UselessPickles/diamondtel-m92-bluetooth/microcontroller/DiamondTelM92Bluetooth.X/src/bluetooth/bt_command_send.c

/******************************************************************************
 Software License Agreement:

 The software supplied herewith by Microchip Technology Incorporated
 (the "Company") for its PICmicro(r) Microcontroller is intended and
 supplied to you, the Company's customer, for use solely and
 exclusively on Microchip PICmicro Microcontroller products. The
 software is owned by the Company and/or its supplier, and is
 protected under applicable copyright laws. All rights are reserved.
 Any use in violation of the foregoing restrictions may subject the
 user to criminal sanctions under applicable laws, as well as to
 civil liability for the breach of the terms and conditions of this
 license.

 THIS SOFTWARE IS PROVIDED IN AN "AS IS" CONDITION. NO WARRANTIES,
 WHETHER EXPRESS, IMPLIED OR STATUTORY, INCLUDING, BUT NOT LIMITED
 TO, IMPLIED WARRANTIES OF MERCHANTABILITY AND FITNESS FOR A
 PARTICULAR PURPOSE APPLY TO THIS SOFTWARE. THE COMPANY SHALL NOT,
 IN ANY CIRCUMSTANCES, BE LIABLE FOR SPECIAL, INCIDENTAL OR
 CONSEQUENTIAL DAMAGES, FOR ANY REASON WHATSOEVER.
********************************************************************/
#include "bt_command_send.h"
#include "bt_command_decode.h"
#include "atcmd.h"
#include <xc.h>
#include <string.h>
#include <stdio.h>
#include "../../mcc_generated_files/uart2.h"
#include "../../mcc_generated_files/pin_manager.h"
#include "../app.h"

#define ACK_TIME_OUT_MS                 1000
#define APP_INPUT_WAITING_TIME_OUT_MS   100
#define INTERVAL_AFTER_ACK_CMD          20
#define QUEQUED_CMD_MAX                 20

static struct {
    uint8_t SendingCmdNum;
    struct{
        uint16_t startBufPt;
        uint16_t endBufPt;
        uint16_t cmdSize;
        uint8_t cmdID;
		uint8_t cmdInfo;
        CMD_PROCESSING_STATUS cmdStatus;
    } SendingCmdArray[QUEQUED_CMD_MAX];
} BT_SendingCmd;

#define UR_TX_BUF_SIZE              400
static uint8_t          UR_TxBuf[UR_TX_BUF_SIZE];
static uint16_t         UR_TxBufHead;
static uint16_t         UR_TxBufTail;
static uint16_t         UR_TxBufTail2;
typedef enum {
	TXRX_BUF_EMPTY,
	TXRX_BUF_OK,
	TXRX_BUF_FULL
} TXRX_BUF_STATUS;
static TXRX_BUF_STATUS  UR_TxBufStatus;

typedef enum {
    BT_CMD_SEND_STATE_IDLE = 0,         //no data in the queue, MFB is low
    BT_CMD_SEND_MFB_HIGH_WAITING,       //set MFB to high, and wait for 2ms
    BT_CMD_SEND_DATA_SENDING,           //UART interface is working
    BT_CMD_SEND_ACK_WAITING,            //waiting for ack
    BT_CMD_SEND_ACK_ERROR,
    BT_CMD_SEND_ACK_OK,
} BT_CMD_SEND_STATE;
BT_CMD_SEND_STATE BT_CMD_SendState;
uint16_t BT_CommandSendTimer;//BT_CommandStartMFBWaitTimer;
uint16_t BT_commandOverRun=0;
uint16_t BT_bufferOverRun=0;
uint8_t gatt_status_code=0;

static bool copyCommandToBuffer(uint8_t* data, uint16_t size, uint8_t cmdInfo);
static bool StartRegisterNewCommand(uint16_t start_index, uint16_t cmd_size, uint8_t cmd_id, uint8_t cmd_info);
static bool EndRegisterNewCommand(uint16_t end_index);
static bool RemoveFirstCommand(void);

/*======================================*/
/*  function implemention  */
/*======================================*/
void BT_GiveUpThisCommand( void )
{
    RemoveFirstCommand();
}
/*------------------------------------------------------------*/

/*------------------------------------------------------------*/
bool copySendingCommandToBuffer(uint8_t* data, uint16_t size)
{
	return copyCommandToBuffer(data, size, CMD_INFO_MCU);
}
static bool copyCommandToBuffer(uint8_t* data, uint16_t size, uint8_t cmdInfo)
{
    bool buf_result = true;
    uint8_t ur_tx_buf_status_save = UR_TxBufStatus;
    uint16_t ur_tx_buf_head_save = UR_TxBufHead;

	if(UR_TxBufHead > UR_TxBufTail)
	{
		if(UR_TxBufHead - UR_TxBufTail	+ size >= UR_TX_BUF_SIZE)
		{
			BT_bufferOverRun++;
			return false;		
		}
	}	
	else if(UR_TxBufHead < UR_TxBufTail)
	{
		if(UR_TxBufHead + size >=  UR_TxBufTail)
		{
			BT_bufferOverRun++;
			return false;
		}
	}

    if(UR_TxBufStatus !=  TXRX_BUF_FULL)
    {
        if(!StartRegisterNewCommand(UR_TxBufHead, size, data[3], cmdInfo))
        {
            return false;
        }
        
        while(size--)
        {
            UR_TxBuf[UR_TxBufHead++] = *data++;

            if(UR_TxBufHead >= UR_TX_BUF_SIZE)
                UR_TxBufHead = 0;

            if(UR_TxBufHead ==  UR_TxBufTail)
            {
                if(size)
                {
                    buf_result = false;
                    UR_TxBufStatus = ur_tx_buf_status_save;		//restore in this case
                    UR_TxBufHead = ur_tx_buf_head_save;                 //restore in this case
                }
                else
                {
                    UR_TxBufStatus =  TXRX_BUF_FULL;            //test this code
                }
                break;
            }
            else
            {
                UR_TxBufStatus = TXRX_BUF_OK;
            }
        }

        if(buf_result)
        {
            EndRegisterNewCommand(UR_TxBufHead);
        }
    }
    else
    {
        buf_result = false;
    }
    return buf_result;
}

/*------------------------------------------------------------*/

uint8_t BT_CalculateCmdChecksum(uint8_t const* startByte, uint8_t const* endByte)
{
    uint8_t checksum = 0;
    while(startByte <= endByte)
    {
        checksum += *startByte;
        startByte++;
    }
    checksum = ~checksum + 1;
    return checksum;
}

void BT_SendBytesAsCompleteCommand(uint8_t const* command, uint8_t command_length)
{
    copySendingCommandToBuffer(command, command_length);
}

/*------------------------------------------------------------*/

void BT_ResetEEPROM(void) {
  BT_MMI_ActionCommand(RESET_EEPROM_SETTING, BT_linkIndex);
}

void BT_SetEventMask(void) {
  uint8_t command[9];
  command[0] = 0xAA;                      //header byte 0
  command[1] = 0x00;                      //header byte 1
  command[2] = 5;                      //length
  command[3] = REPORT_MASK;        	//command ID
  command[4] = 0b00111011;
  command[5] = 0b01110000;     
  command[6] = 0b11110101;     
  command[7] = 0b11111111;     
  command[8] = BT_CalculateCmdChecksum(&command[2], &command[7]);
  copySendingCommandToBuffer(command, 9);  
}

void BT_ReadLinkedDeviceName(void) {
  uint8_t command[7];
  command[0] = 0xAA;                      //header byte 0
  command[1] = 0x00;                      //header byte 1
  command[2] = 3;                      //length
  command[3] = READ_LINKED_DEVICE_INFOR;   	//command ID
  command[4] = BT_linkIndex; // link_index, set to 0
  command[5] = 0; // 0 = read device name
  command[6] = BT_CalculateCmdChecksum(&command[2], &command[5]);
  copySendingCommandToBuffer(command, 7);  
}

void BT_ReadLocalBDAddress(void) {
  uint8_t command[7];
  command[0] = 0xAA;                      //header byte 0
  command[1] = 0x00;                      //header byte 1
  command[2] = 3;                      //length
  command[3] = READ_LOCAL_BD_ADDR;   	//command ID
  command[4] = BT_linkIndex; // link_index, set to 0
  command[5] = 0; // 0 = read device name
  command[6] = BT_CalculateCmdChecksum(&command[2], &command[5]);
  copySendingCommandToBuffer(command, 7);  
}

void BT_ReadDeviceName(void) {
  uint8_t command[6];
  command[0] = 0xAA;                      //header byte 0
  command[1] = 0x00;                      //header byte 1
  command[2] = 2;                      //length
  command[3] = READ_LOCAL_DEVICE_NAME;   	//command ID
  command[4] = 0; // reserved (set to zero)
  command[5] = BT_CalculateCmdChecksum(&command[2], &command[4]);
  copySendingCommandToBuffer(command, 6);  
}

bool BT_SetDeviceName(char const* name) {
  size_t len = strlen(name);
  
  if (len > BT_MAX_DEVICE_NAME_LENGTH) {
    return false;
  }
  
  uint8_t command[BT_MAX_DEVICE_NAME_LENGTH + 8];
  command[0] = 0xAA;      //header byte 0
  command[1] = 0x00;      //header byte 1
  command[2] = len + 4;      //length
  command[3] = CONFIGURE_VENDOR_PARAMETER;      //command ID
  command[4] = 0;      // op code: 0 = set device name
  command[5] = 0;      // option (reserved): set to zero
  command[6] = len;      // device name length


  memcpy(command + 7, name, len);

  command[len + 7] = BT_CalculateCmdChecksum(&command[2], &command[len + 6]);
	return copySendingCommandToBuffer(command, len + 8); 
}

bool BT_SetPinCode(uint8_t digit1, uint8_t digit2, uint8_t digit3, uint8_t digit4) {
  uint8_t command[9];
  command[0] = 0xAA;      //header byte 0
  command[1] = 0x00;      //header byte 1
  command[2] = 5;      //length
  command[3] = CHANGE_PIN_CODE;      //command ID
  command[4] = '0' + digit1;
  command[5] = '0' + digit2;
  command[6] = '0' + digit3;
  command[7] = '0' + digit4;
  command[8] = BT_CalculateCmdChecksum(&command[2], &command[7]);
	return copySendingCommandToBuffer(command, 9); 
}

void BT_StartVoiceCommand(void) {
  BT_MMI_ActionCommand(VOICE_DIAL, BT_linkIndex);
}

void BT_CancelVoiceCommand(void) {
  BT_MMI_ActionCommand(CANCEL_VOICE_DIAL, BT_linkIndex);
}

bool BT_MakeCall(char const* number) {
  printf("[CALL] Make Call: %s\r\n", number);
  
  size_t len = strlen(number);
  
  if (len > 19) {
    return false;
  }
  
  uint8_t command[25];
  command[0] = 0xAA;      //header byte 0
  command[1] = 0x00;      //header byte 1
  command[2] = len + 2;      //length
  command[3] = MAKE_CALL;      //command ID
  command[4] = BT_linkIndex;      //link_index, set to 0

  memcpy(command + 5, number, len);

  command[len + 5] = BT_CalculateCmdChecksum(&command[2], &command[len + 4]);
	return copySendingCommandToBuffer(command, len + 6);
}

void BT_SetMicrohponeMuted(bool isMuted) {
  BT_MMI_ActionCommand(isMuted ? MUTE_MIC : UNMUTE_MIC, BT_linkIndex);
}

void BT_EndCall(void) {
  printf("[CALL] End Call\r\n");
  BT_MMI_ActionCommand(FORCE_END_CALL, BT_linkIndex);
}

void BT_AcceptCall(void) {
  printf("[CALL] Accept Call\r\n");
  BT_MMI_ActionCommand(ACCEPT_CALL, BT_linkIndex);
}

void BT_RejectCall(void) {
  printf("[CALL] Reject Call\r\n");
  BT_MMI_ActionCommand(REJECT_CALL, BT_linkIndex);
}

void BT_SwapHoldOrWaitingCall(void) {
  printf("[CALL] Swap Hold/Waiting Call\r\n");
  BT_MMI_ActionCommand(ACTIVE_CALL_HOLD_ACCEPT_HELD_CALL, BT_linkIndex);
}

void BT_EndHoldOrWaitingCall(void) {
  printf("[CALL] End Hold/Waiting Call\r\n");
  BT_MMI_ActionCommand(RELEASE_CALL, BT_linkIndex);
}

void BT_SwapHoldOrWaitingCallAndEndActiveCall(void) {
  printf("[CALL] Swap Hold/Waiting Call + End Active Call\r\n");
  BT_MMI_ActionCommand(ACCEPT_WAITING_HOLD_CALL_RLS_ACTIVE_CALL, BT_linkIndex);
}

void BT_EnterPairingMode(void) {
  printf("[PAIR] Enter\r\n");
  BT_MMI_ActionCommand(ANY_MODE_ENTERING_PAIRING, 0);
}

void BT_ExitPairingMode(void) {
  printf("[PAIR] Exit\r\n");
  BT_MMI_ActionCommand(EXIT_PAIRING_MODE, 0);
}

void BT_MMI_ActionCommand(uint8_t MMI_ActionCode, uint8_t link_index)
{
	BT_Send_ActionCommand(MMI_ActionCode, link_index, CMD_INFO_MCU);
}

void BT_Send_ActionCommand(uint8_t MMI_ActionCode, uint8_t link_index, uint8_t cmd_info)
{
    uint8_t command[8];
    command[0] = 0xAA;      //header byte 0
    command[1] = 0x00;      //header byte 1
    command[2] = 0x03;      //length
    command[3] = MMI_CMD;      //command ID
    command[4] = link_index;      //link_index
    command[5] = MMI_ActionCode;
    command[6] = BT_CalculateCmdChecksum(&command[2], &command[5]);
  	copyCommandToBuffer(&command[0], 7, cmd_info);
    //CommandAckStatus.MMI_ACTION_status = COMMAND_IS_SENT;
}

/*------------------------------------------------------------*/
void BT_SendAckToEvent(uint8_t ack_event)
{
    uint8_t command[6];
    command[0] = 0xAA;                      //header byte 0
    command[1] = 0x00;                      //header byte 1
    command[2] = 0x02;                      //length
    command[3] = MCU_SEND_EVENT_ACK;        //command ID
    command[4] = ack_event;                 //event to ack
    command[5] = BT_CalculateCmdChecksum(&command[2], &command[4]);
    copySendingCommandToBuffer(&command[0], 6);
}

/*------------------------------------------------------------*/
void BT_LinkBackToLastDevice(void)
{
    printf("[LINKBACK] Start\r\n");
    uint8_t command[6];
    command[0] = 0xAA;                      //header byte 0
    command[1] = 0x00;                      //header byte 1
    command[2] = 0x02;                      //length
    command[3] = PROFILE_LINK_BACK;         //command ID
    command[4] = 0x01;                      //0x00: last device, 0x01: last HFP device, 0x02: last A2DP device
    command[5] = BT_CalculateCmdChecksum(&command[2], &command[4]);
    copySendingCommandToBuffer(&command[0], 6);
   // CommandAckStatus.LINK_BACK_status = COMMAND_IS_SENT;
}

/*------------------------------------------------------------*/
void BT_CancelLinkback(void)
{
    uint8_t command[6];
    command[0] = 0xAA;                      //header byte 0
    command[1] = 0x00;                      //header byte 1
    command[2] = 0x02;                      //length
    command[3] = DISCONNECT;                //command ID
    command[4] = 0x01;                      
    command[5] = BT_CalculateCmdChecksum(&command[2], &command[4]);
    copySendingCommandToBuffer(&command[0], 6);
}

/*------------------------------------------------------------*/
void BT_DisconnectAllProfile(void)
{
    uint8_t command[6];
    command[0] = 0xAA;                      //header byte 0
    command[1] = 0x00;                      //header byte 1
    command[2] = 0x02;                      //length
    command[3] = DISCONNECT;                //command ID
    command[4] = 0x0f;                      //event to ack
    command[5] = BT_CalculateCmdChecksum(&command[2], &command[4]);
    copySendingCommandToBuffer(&command[0], 6);
}
/*------------------------------------------------------------*/
void BT_SetHFPGain(uint8_t gain)
{
    uint8_t command[7];
    command[0] = 0xAA;                      //header byte 0
    command[1] = 0x00;                      //header byte 1
    command[2] = 0x03;                    //length
    command[3] = SET_HF_GAIN_LEVEL;                //command ID
    command[4] = BT_linkIndex;                      //link index
    command[5] = gain & 0x0f;
    command[6] = BT_CalculateCmdChecksum(&command[2], &command[5]);
  	copyCommandToBuffer(&command[0], 7, CMD_INFO_MCU);
}

/*------------------------------------------------------------*/
void BT_SetAecEnabled(bool isEnabled) {
  BT_MMI_ActionCommand(isEnabled ? ENABLE_AEC : DISABLE_AEC, BT_linkIndex);
}

/*------------------------------------------------------------*/
void BT_CommandSend_Initialize( void )
{
    UR_TxBufHead = 0;
    UR_TxBufTail = 0;
    UR_TxBufStatus = TXRX_BUF_EMPTY;
    BT_SendingCmd.SendingCmdNum = 0;
}

/*------------------------------------------------------------*/
void BT_CommandSend_Task( void )
{
    switch(BT_CMD_SendState)
    {
        case BT_CMD_SEND_STATE_IDLE:
            if(BT_SendingCmd.SendingCmdNum)
            {
                //IO_BT_MFB_SetHigh();
                BT_CommandSendTimer = 3;      //wait 2 - 3ms
                BT_CMD_SendState = BT_CMD_SEND_MFB_HIGH_WAITING;
            }
            break;
            
        case BT_CMD_SEND_MFB_HIGH_WAITING:
            if(!BT_CommandSendTimer)
            {
                UART_TransferFirstByte();
                BT_SendingCmd.SendingCmdArray[0].cmdStatus = IN_SENDING;
                BT_CMD_SendState = BT_CMD_SEND_DATA_SENDING;
            }
            break;

        case BT_CMD_SEND_DATA_SENDING:
            //do nothing, UART interrupt will handle
            break;

        case BT_CMD_SEND_ACK_WAITING:       //new
            if(!BT_CommandSendTimer)
            {
                APP_BT_EventHandler(BT_EVENT_CMD_SENT_NO_ACK, (uint16_t)(BT_SendingCmd.SendingCmdArray[0].cmdID),  0);        //send event to user application layer with command id, and event type
                
                if (BT_SendingCmd.SendingCmdArray[0].cmdID == VENDOR_AT_CMD) {
                  ATCMD_BT_ResponseHandler(ATCMD_Response_FAILED);
                }
                
                BT_SendingCmd.SendingCmdArray[0].cmdStatus = ERROR_NO_ACK;
                BT_CommandSendTimer = APP_INPUT_WAITING_TIME_OUT_MS;
                BT_CMD_SendState = BT_CMD_SEND_ACK_ERROR;
            }
            break;
        
        case BT_CMD_SEND_ACK_ERROR:
            if (!BT_CommandSendTimer) {
                if (BT_SendingCmd.SendingCmdNum) {
                    UART_TransferFirstByte();
                    BT_SendingCmd.SendingCmdArray[0].cmdStatus = IN_SENDING;
                    BT_CMD_SendState = BT_CMD_SEND_DATA_SENDING; //re-sending last command or sending next command
                } else {
                    // BM6X_MFB_SetLow();
                    BT_CMD_SendState = BT_CMD_SEND_STATE_IDLE;
                }
            }
            break;
       
        case BT_CMD_SEND_ACK_OK:
            if (!BT_CommandSendTimer) {
                RemoveFirstCommand();
                if (BT_SendingCmd.SendingCmdNum) {
                    UART_TransferFirstByte();
                    BT_SendingCmd.SendingCmdArray[0].cmdStatus = IN_SENDING;
                    BT_CMD_SendState = BT_CMD_SEND_DATA_SENDING;
                } else {
                    //IO_BT_MFB_SetLow();
                    BT_CMD_SendState = BT_CMD_SEND_STATE_IDLE;
                }
            }
            break;
            
        default:
            break;
    }
}

/*------------------------------------------------------------*/
uint8_t BT_UpdateAckStatusWhenReceived(uint8_t command_id, uint8_t ack_status)
{
  uint8_t params[2] = {
    command_id, ack_status
  };
  
    uint16_t temp;
    if( BT_CMD_SendState == BT_CMD_SEND_ACK_WAITING )
    {
        if(command_id == BT_SendingCmd.SendingCmdArray[0].cmdID)
            BT_SendingCmd.SendingCmdArray[0].cmdStatus = ack_status;

		// Here we can know what is the ACK status 5506 reply to the previous sent command.
        BT_CommandSendTimer = APP_INPUT_WAITING_TIME_OUT_MS;
        BT_CMD_SendState = BT_CMD_SEND_ACK_OK;

		if(command_id == GATT_CTRL)
			gatt_status_code = ack_status;
        
    APP_BT_EventHandler(ack_status == 0 ? BT_EVENT_CMD_SENT_ACK_OK : BT_EVENT_CMD_SENT_ACK_ERROR, (uint16_t)command_id, params);        //send event to user application layer with command id, and event type
    
    if ((ack_status != 0) && (command_id == VENDOR_AT_CMD)) {
      ATCMD_BT_ResponseHandler(ATCMD_Response_FAILED);
    }

		return BT_SendingCmd.SendingCmdArray[0].cmdInfo;
    }
	return CMD_INFO_IGNORE;
}

/*------------------------------------------------------------*/
void BT_CommandSend_Timer1MS_Interrupt(void)
{
    if( BT_CommandSendTimer/*BT_CommandStartMFBWaitTimer*/)
    {
        -- BT_CommandSendTimer/*BT_CommandStartMFBWaitTimer*/;
    }
}

/*------------------------------------------------------------*/
void UART_TransferFirstByte( void )
{
    uint8_t data;
    UR_TxBufTail2 = BT_SendingCmd.SendingCmdArray[0].startBufPt;
    data = UR_TxBuf[UR_TxBufTail2++];
    if(UR_TxBufTail2 >= UR_TX_BUF_SIZE)
            UR_TxBufTail2 = 0;
    UART2_Write(data);
}

/*------------------------------------------------------------*/
void UART_TransferNextByte( void )
{
    uint8_t data;
    if(UR_TxBufTail2 == BT_SendingCmd.SendingCmdArray[0].endBufPt)
    {
        if(BT_CMD_SendState == BT_CMD_SEND_DATA_SENDING)
        {
            if(BT_SendingCmd.SendingCmdArray[0].cmdID != MCU_SEND_EVENT_ACK)
            {
                BT_CommandSendTimer =  ACK_TIME_OUT_MS;
                BT_CMD_SendState = BT_CMD_SEND_ACK_WAITING;
            }
            else        //just sent is ACK_TO_EVENT command
            {
                BT_CommandSendTimer = INTERVAL_AFTER_ACK_CMD;
                BT_SendingCmd.SendingCmdArray[0].cmdStatus = STS_OK;
                BT_CMD_SendState = BT_CMD_SEND_ACK_OK;
            }
        }
    }
    else
    {
        data = UR_TxBuf[UR_TxBufTail2++];
        if(UR_TxBufTail2 >= UR_TX_BUF_SIZE)
            UR_TxBufTail2 = 0;
        UART2_Write(data);
    }
}

static bool StartRegisterNewCommand(uint16_t start_index, uint16_t cmd_size, uint8_t cmd_id, uint8_t cmdInfo)
{
    if(!cmd_size)
        return false;
    
    if(BT_SendingCmd.SendingCmdNum < QUEQUED_CMD_MAX)
    {
        BT_SendingCmd.SendingCmdArray[BT_SendingCmd.SendingCmdNum].startBufPt = start_index;
        BT_SendingCmd.SendingCmdArray[BT_SendingCmd.SendingCmdNum].cmdSize = cmd_size;
        BT_SendingCmd.SendingCmdArray[BT_SendingCmd.SendingCmdNum].cmdID = cmd_id;
        BT_SendingCmd.SendingCmdArray[BT_SendingCmd.SendingCmdNum].cmdInfo = cmdInfo;

        if(cmd_id!=0x1f)
            Nop();
        return true;
    }
    else
    {
	    BT_commandOverRun++;
        return false;
    }
}

static bool EndRegisterNewCommand(uint16_t end_index)
{
    if(BT_SendingCmd.SendingCmdNum < QUEQUED_CMD_MAX)
    {
        BT_SendingCmd.SendingCmdArray[BT_SendingCmd.SendingCmdNum].endBufPt = end_index;
        BT_SendingCmd.SendingCmdArray[BT_SendingCmd.SendingCmdNum].cmdStatus = IN_QUEUE;
        BT_SendingCmd.SendingCmdNum++;
    }
    return true;
}

static bool RemoveFirstCommand(void)//index starting from 0
{
    uint8_t i;
    if(!BT_SendingCmd.SendingCmdNum)
        return false;            //parameter error
    
    if(BT_SendingCmd.SendingCmdNum == 1)
    {
        BT_SendingCmd.SendingCmdNum--;
        UR_TxBufTail = UR_TxBufTail2;
        if (UR_TxBufHead == UR_TxBufTail)
            UR_TxBufStatus = TXRX_BUF_EMPTY;
        else
            UR_TxBufStatus = TXRX_BUF_OK;
        return true;
    }
    
    for(i = 0; i < BT_SendingCmd.SendingCmdNum - 1; i++)
    {
        //copy next command info to previous one
        BT_SendingCmd.SendingCmdArray[i].cmdSize = BT_SendingCmd.SendingCmdArray[i + 1].cmdSize;
        BT_SendingCmd.SendingCmdArray[i].cmdStatus = BT_SendingCmd.SendingCmdArray[i + 1].cmdStatus;
        BT_SendingCmd.SendingCmdArray[i].endBufPt = BT_SendingCmd.SendingCmdArray[i + 1].endBufPt;
        BT_SendingCmd.SendingCmdArray[i].startBufPt = BT_SendingCmd.SendingCmdArray[i + 1].startBufPt;
        BT_SendingCmd.SendingCmdArray[i].cmdID = BT_SendingCmd.SendingCmdArray[i + 1].cmdID;
        BT_SendingCmd.SendingCmdArray[i].cmdInfo = BT_SendingCmd.SendingCmdArray[i + 1].cmdInfo;

    }
    BT_SendingCmd.SendingCmdNum--;
    UR_TxBufTail = UR_TxBufTail2;
    if (UR_TxBufHead == UR_TxBufTail)
        UR_TxBufStatus = TXRX_BUF_EMPTY;
    else
        UR_TxBufStatus = TXRX_BUF_OK;
    return true;
}
