UselessPickles/diamondtel-m92-bluetooth/microcontroller/DiamondTelM92Bluetooth.X/src/sound/ringtone.h

/** 
 * @file
 * @author Jeff Lau
 */

#ifndef RINGTONE_H
#define	RINGTONE_H

#ifdef	__cplusplus
extern "C" {
#endif
 
typedef enum RINGTONE_Type {
  RINGTONE_Type_HARSH,
  RINGTONE_Type_SMOOTH,
  RINGTONE_Type_NOKIA,
  RINGTONE_Type_AXEL_F,
  RINGTONE_Type_MEGALOMANIA,
  RINGTONE_Type_CAR_PHONE_SONG,
  RINGTONE_Type_TETRIS,
} RINGTONE_Type;

#define RINGTONE_COUNT (7)

char const* RINGTONE_GetName(RINGTONE_Type ringtone);

void RINGTONE_Start(RINGTONE_Type ringtone);

void RINGTONE_Stop(void);

#ifdef	__cplusplus
}
#endif

#endif	/* RINGTONE_H */
